mgesteiro/EEI-Stopwatch/3D/chasis.png

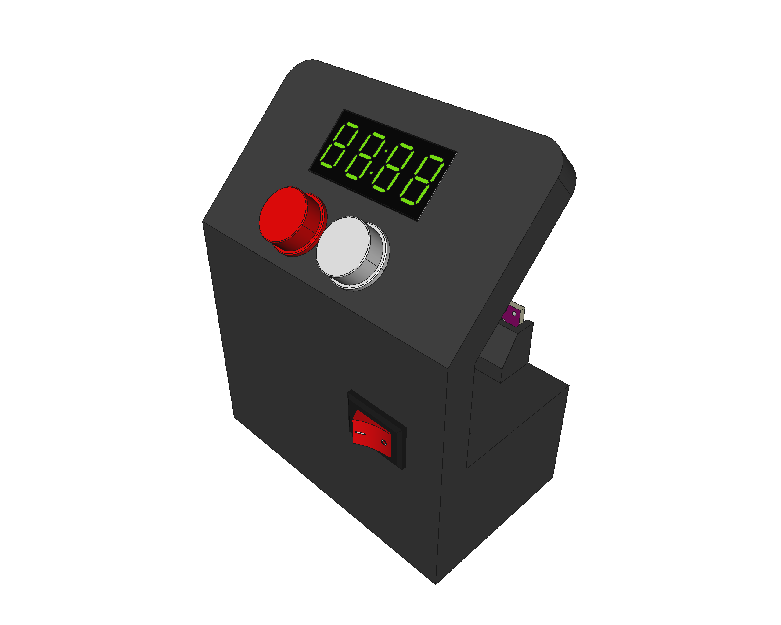
3D/chasis.png
