mgesteiro/EEI-Stopwatch/3D/powerbank.png

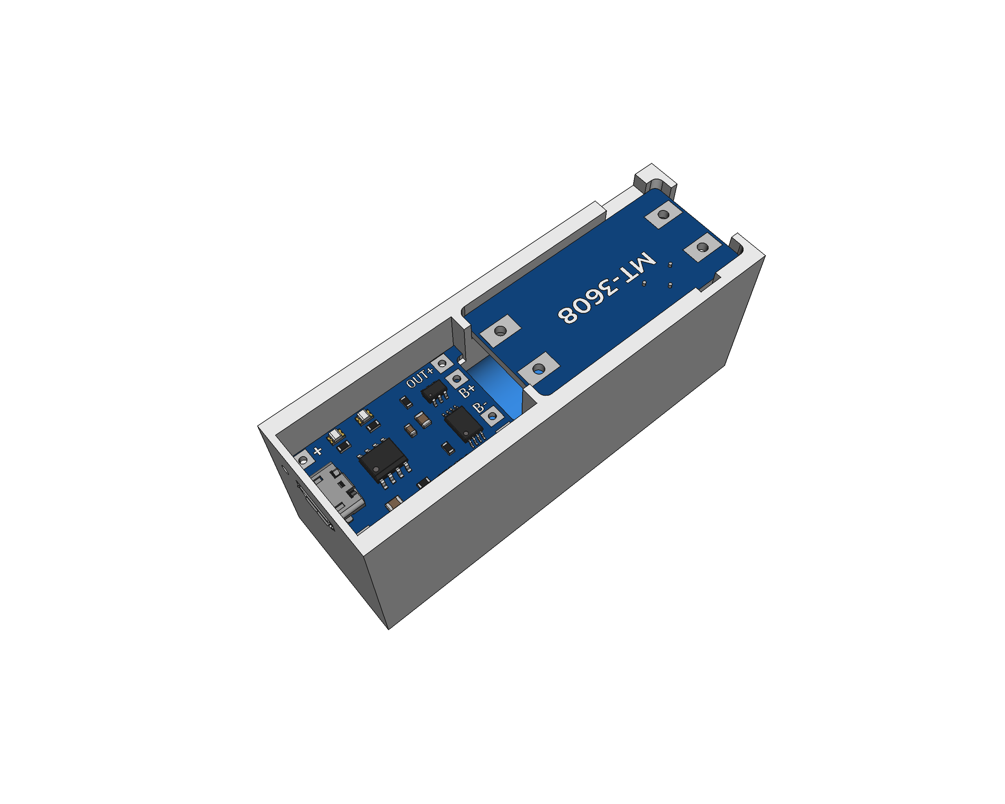
3D/powerbank.png
