mgesteiro/EEI-Stopwatch/electronics/EEI-Stopwatch_bb.png

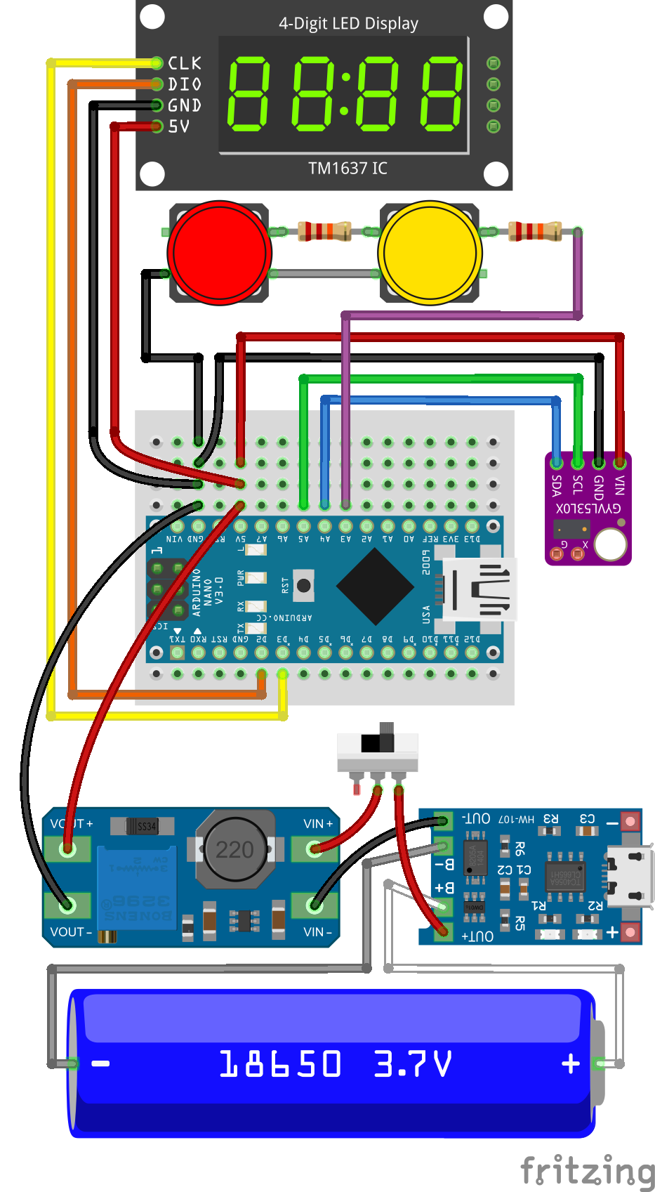
electronics/EEI-Stopwatch_bb.png
